MOSH-Insa-Toulouse/2024-2025-4GP-alienor-jarry-fbm1112/Appli_Android/APP_Boutons_2.png

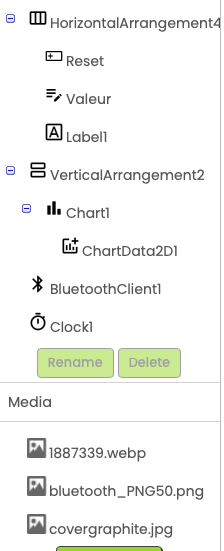
Appli_Android/APP_Boutons_2.png
