MOSH-Insa-Toulouse/2024-2025-4GP-alienor-jarry-fbm1112/LTspice/LTC_suite.asc

C1: cap; 100n
C2: cap; 1µ
C4: cap; 100n
C5: cap; 1p
R1: res; 10k
R2: res; 100k
R3: res; 1k
R4: res; 100k
R5: res; 1k
U1: LTC1050
V1: voltage; 5
V2: voltage; SINE(0 325 50)
V3: voltage; PULSE(0 1 0.2 0.1 0.1 20); AC 1
X1: capteur
Named nets: 0, ADC, Vem, Vep, +5V
.tran 2
;ac dec 100 1 1G
